ArafatBabar/MAGSENSE/Images/IMG_20260801_172510.png

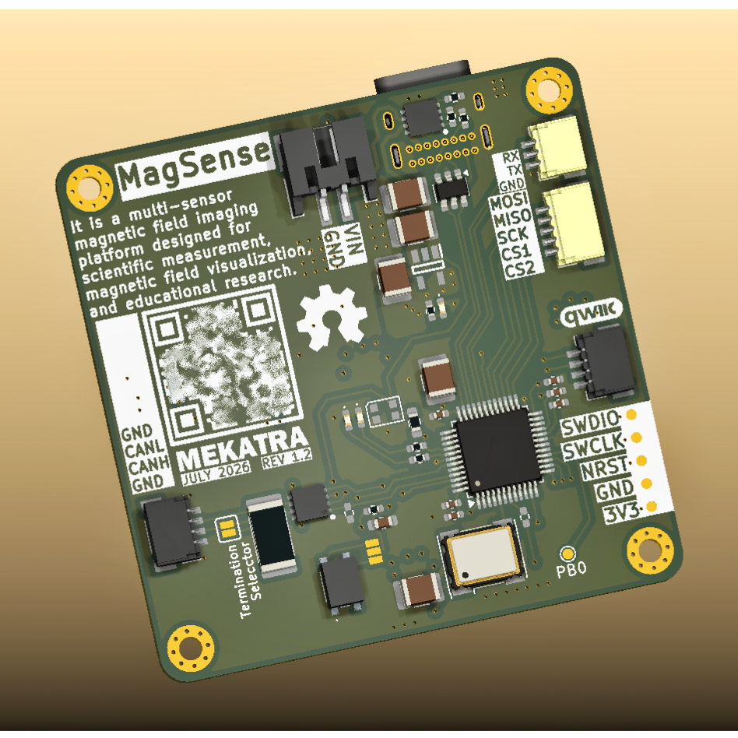
Images/IMG_20260801_172510.png
